SuperHouse/CBMINI/Images/2018-04-11_12-32-10.jpg

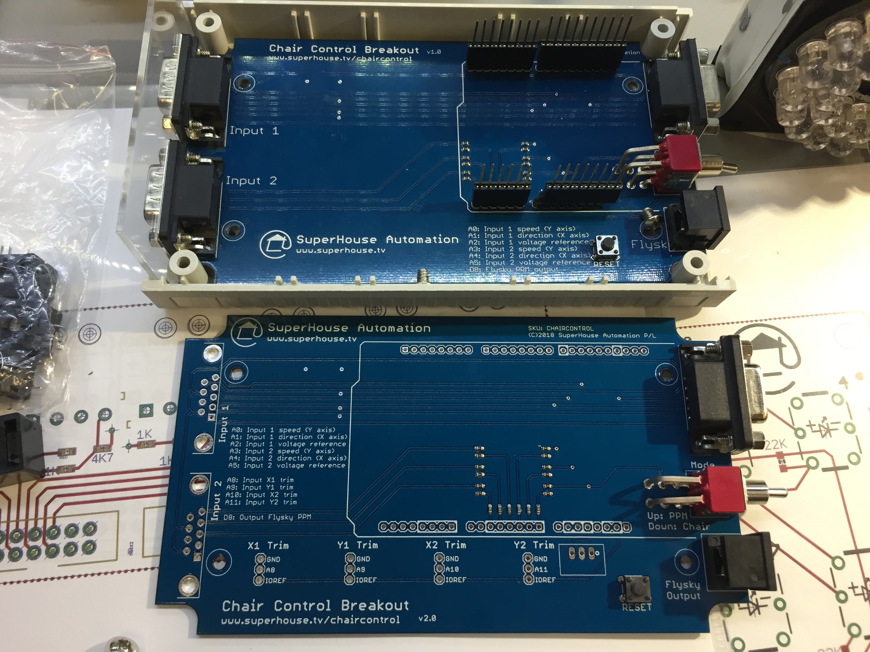
Images/2018-04-11_12-32-10.jpg
