SuperHouse/CBMINI/Images/2018-04-11_17-02-50.jpg

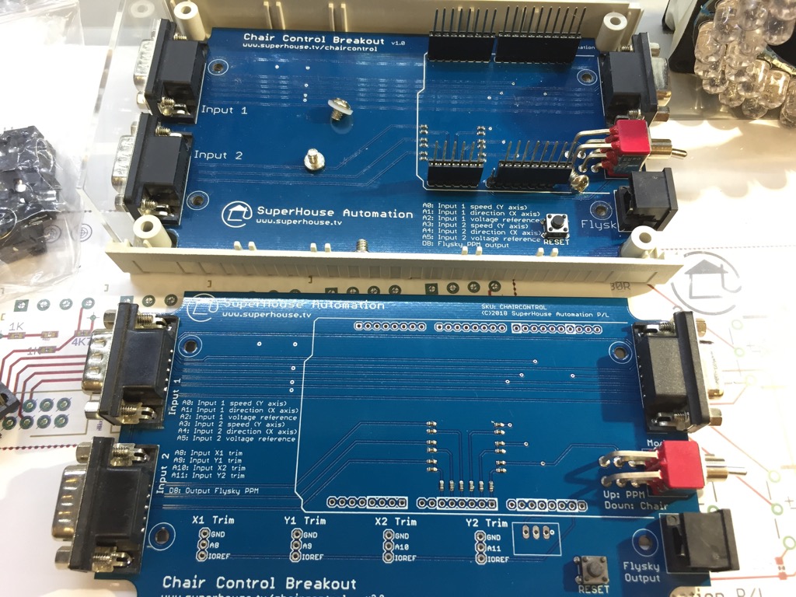
Images/2018-04-11_17-02-50.jpg
