SuperHouse/CBMINI/Images/2018-07-26_15-38-04.jpg

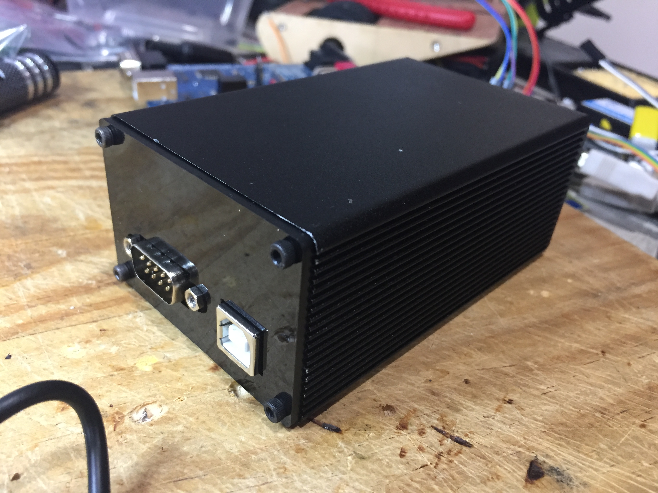
Images/2018-07-26_15-38-04.jpg
