SuperHouse/CBMINI/Images/2018-07-26_15-38-23.jpg

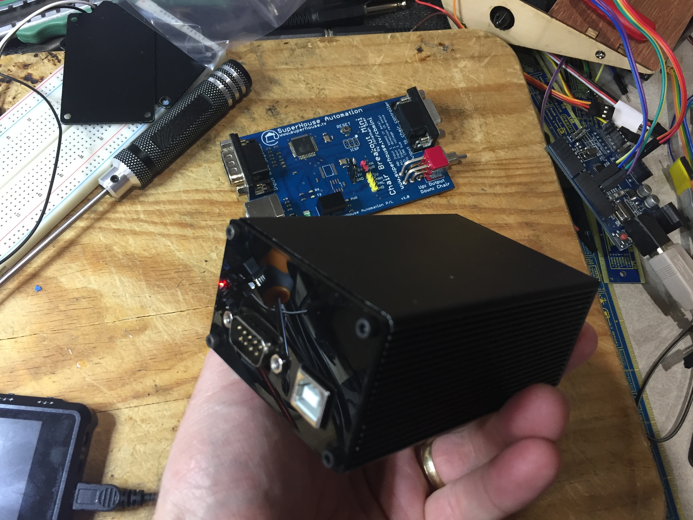
Images/2018-07-26_15-38-23.jpg
