SuperHouse/CBMINI/Images/2018-07-26_15-39-45.jpg

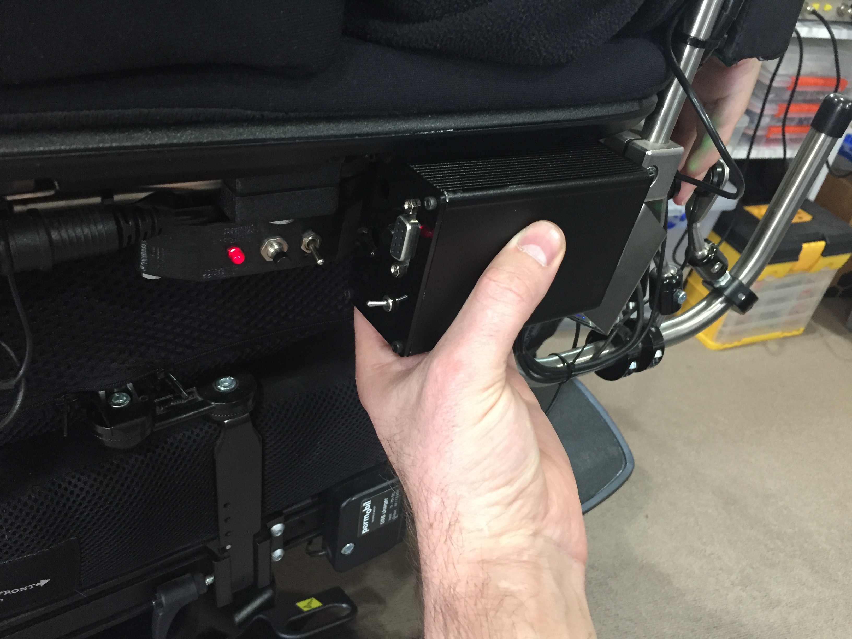
Images/2018-07-26_15-39-45.jpg
