SuperHouse/CBMINI/Images/2018-07-26_15-40-40.jpg

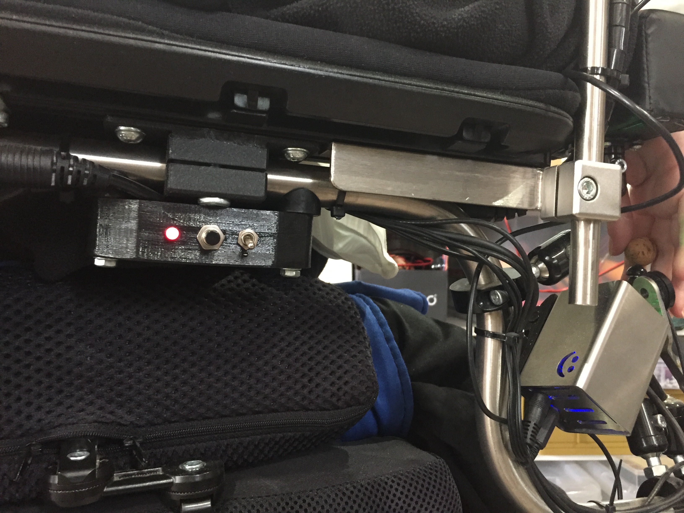
Images/2018-07-26_15-40-40.jpg
