SuperHouse/CBMINI/Images/2018-07-26_15-41-06.jpg

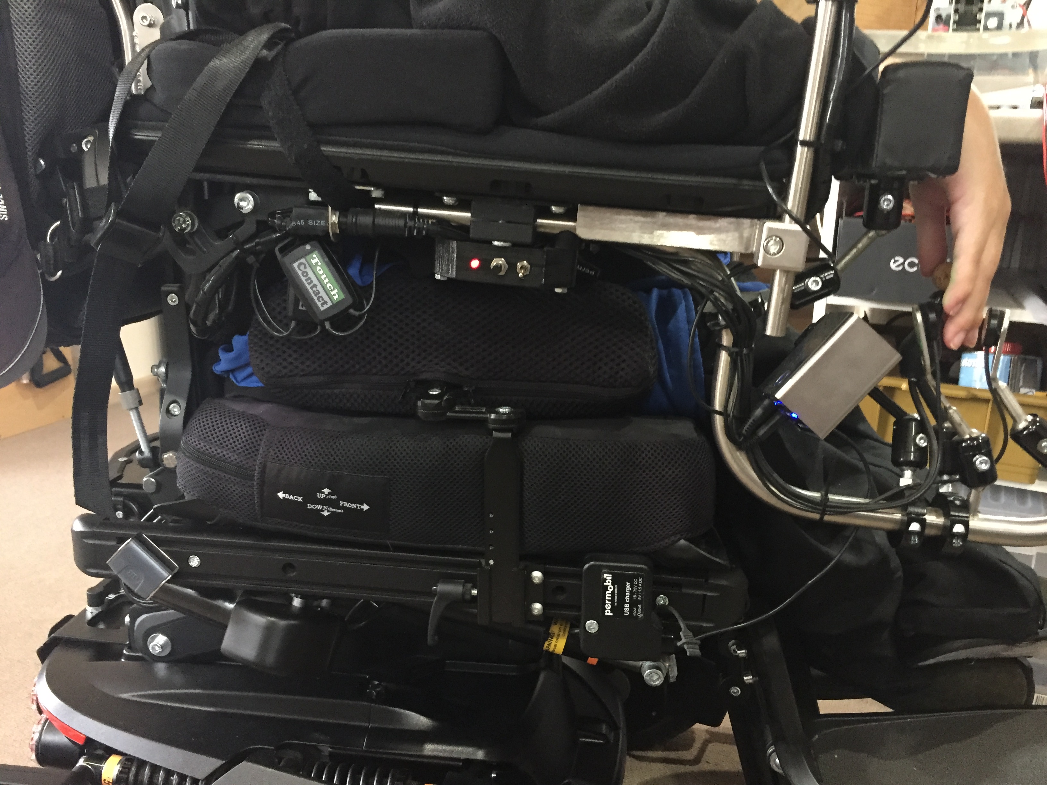
Images/2018-07-26_15-41-06.jpg
