SuperHouse/CBMINI/Images/2018-07-26_15-42-06.jpg

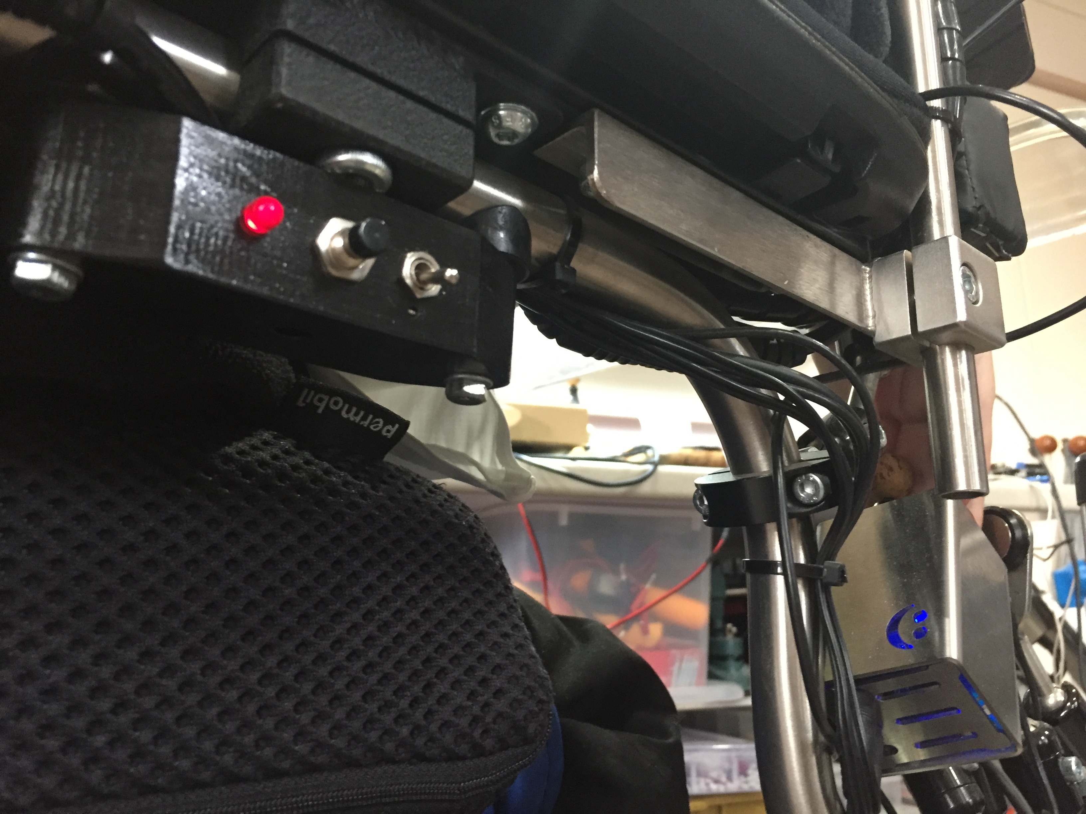
Images/2018-07-26_15-42-06.jpg
