SuperHouse/CBMINI/Images/2018-07-26_15-44-15.jpg

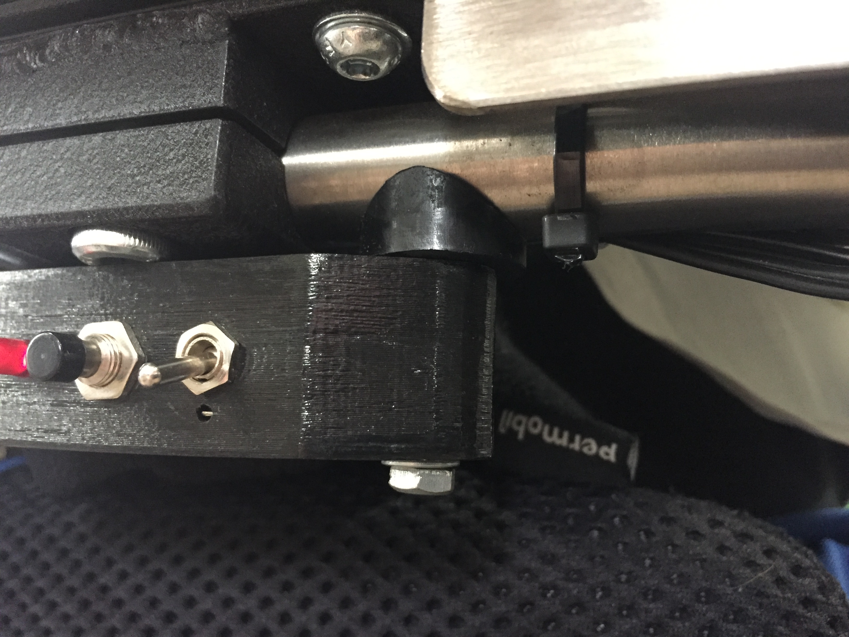
Images/2018-07-26_15-44-15.jpg
