SuperHouse/CBMINI/Images/2018-07-26_15-45-27.jpg

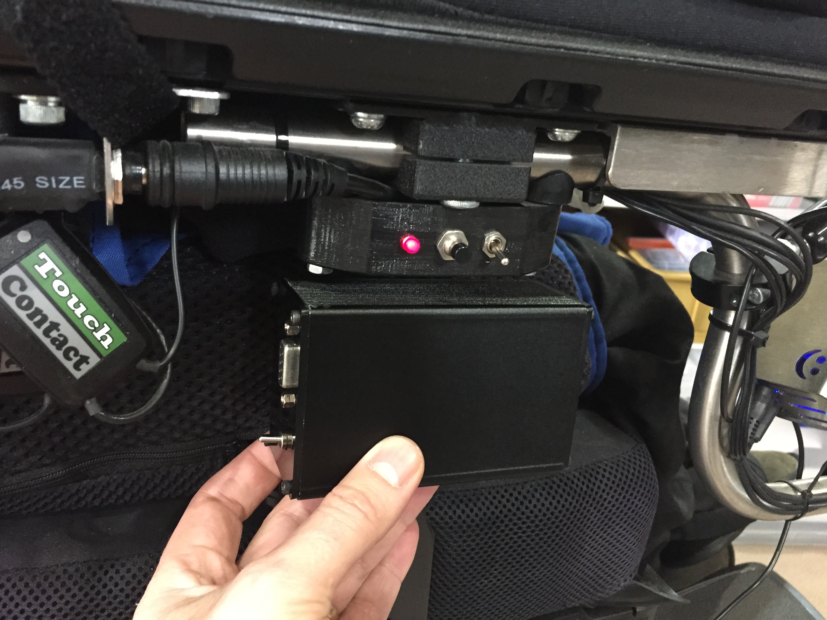
Images/2018-07-26_15-45-27.jpg
