SuperHouse/CBMINI/Images/2018-07-26_16-08-34.jpg

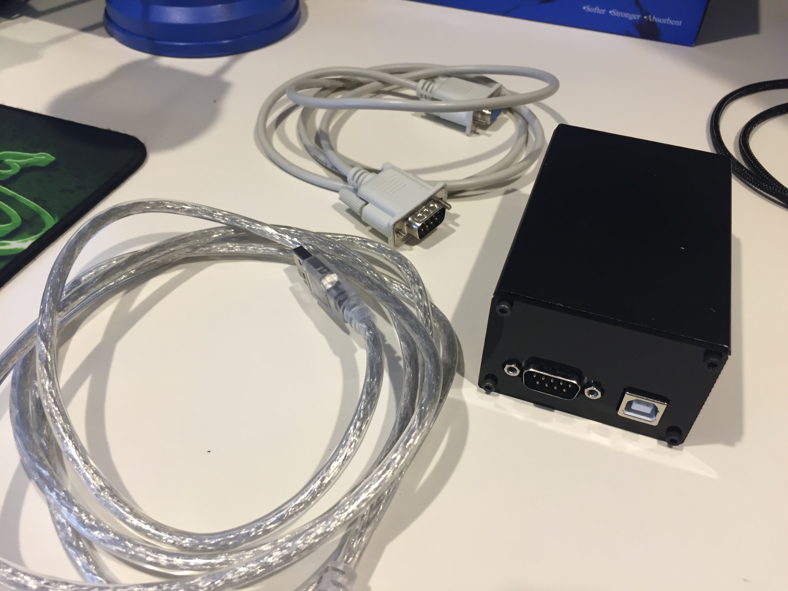
Images/2018-07-26_16-08-34.jpg
