SuperHouse/CBMINI/Images/2018-07-31_14-34-46.jpg

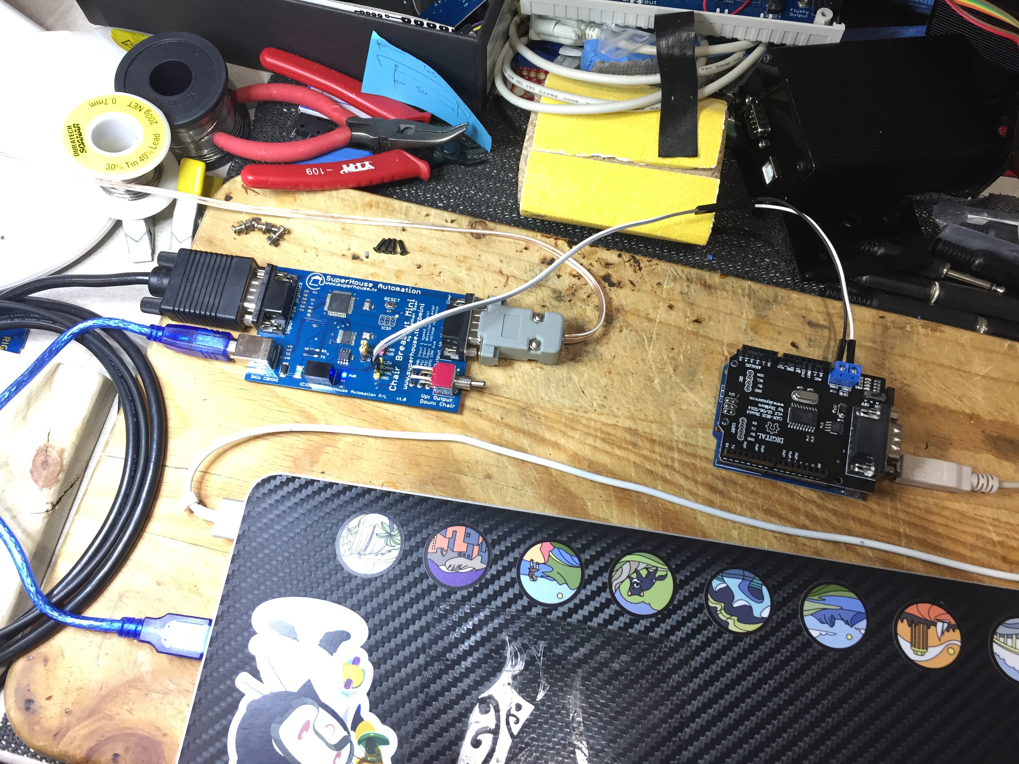
Images/2018-07-31_14-34-46.jpg
