SuperHouse/CBMINI/Images/2018-08-02_20-13-39.jpg

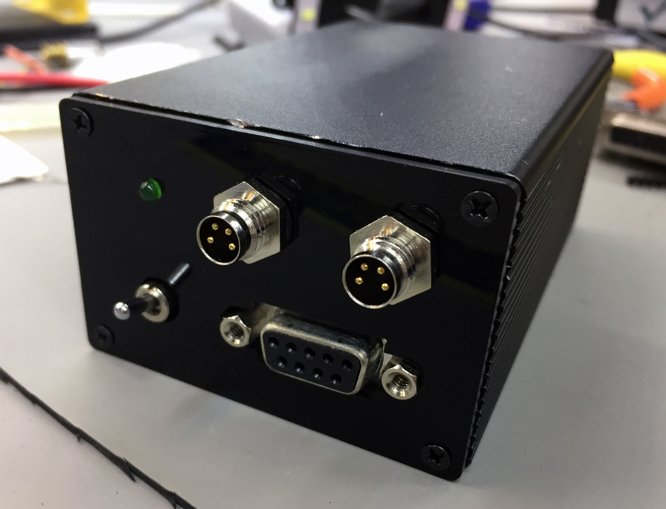
Images/2018-08-02_20-13-39.jpg
