SuperHouse/CBMINI/Images/2019-01-18_22-05-54.jpg

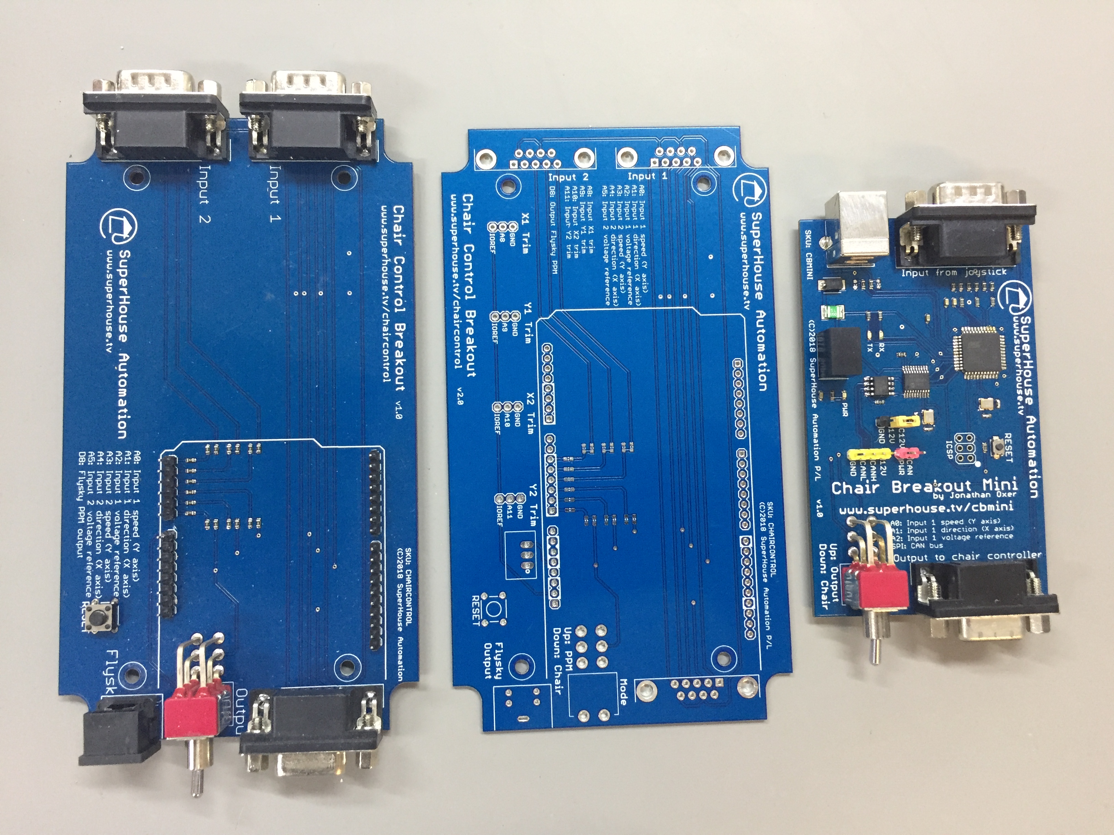
Images/2019-01-18_22-05-54.jpg
