SuperHouse/CBMINI/Images/2019-04-17_09-52-04.jpg

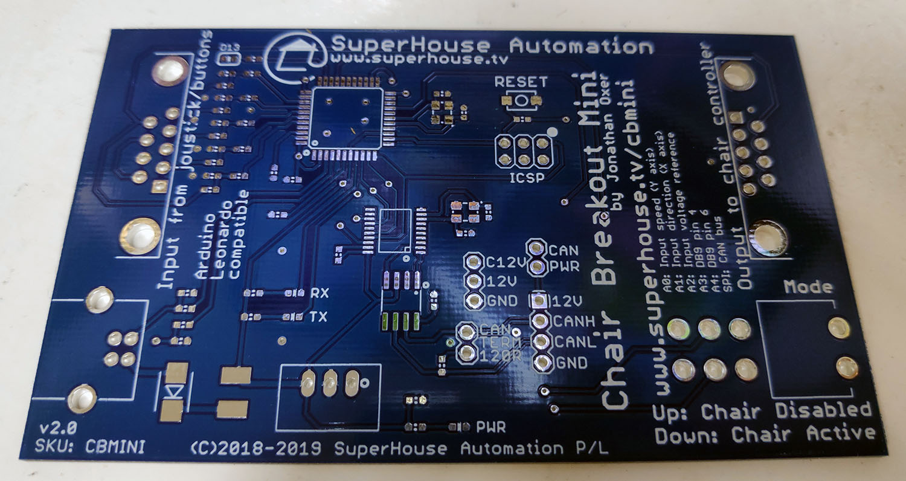
Images/2019-04-17_09-52-04.jpg
