SuperHouse/CBMINI/Images/2019-04-18_10-50-11.jpg

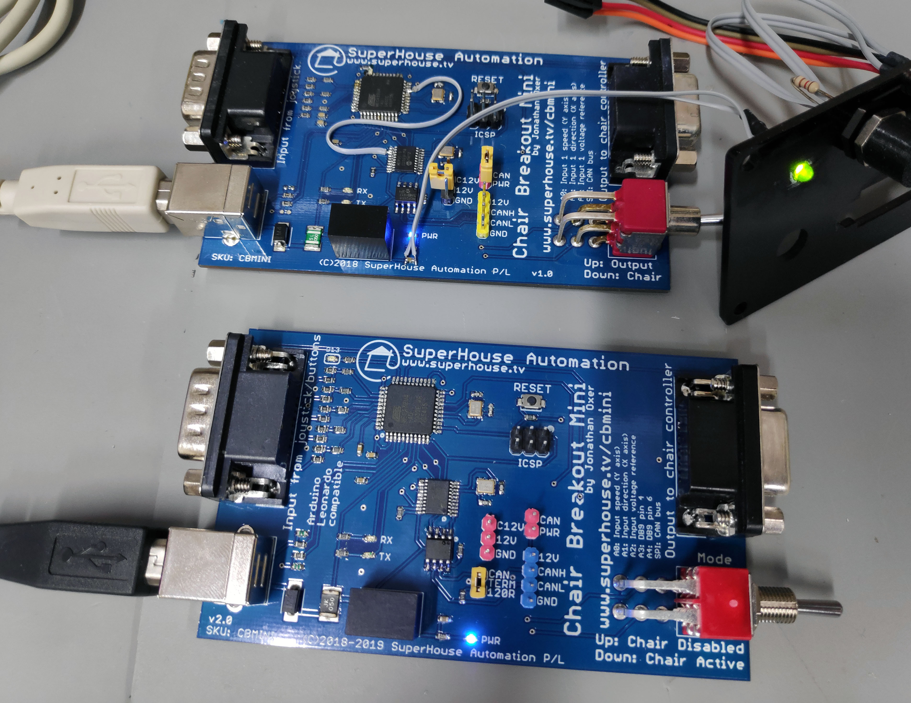
Images/2019-04-18_10-50-11.jpg
