SuperHouse/CBMINI/Images/2019-04-18_11-13-38.jpg

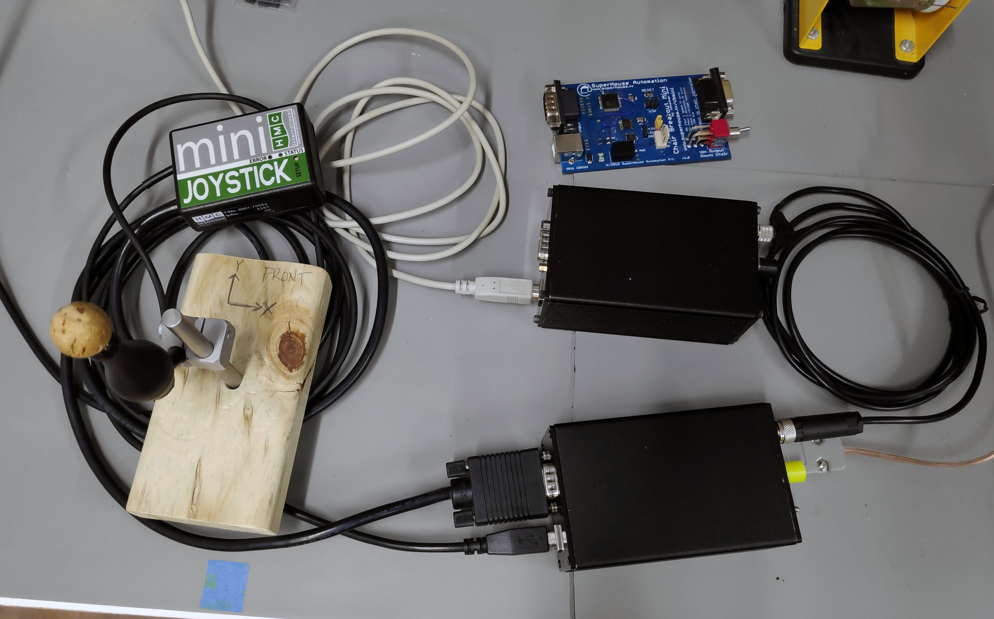
Images/2019-04-18_11-13-38.jpg
