SuperHouse/CBMINI/Images/2019-04-23_15-40-32.jpg

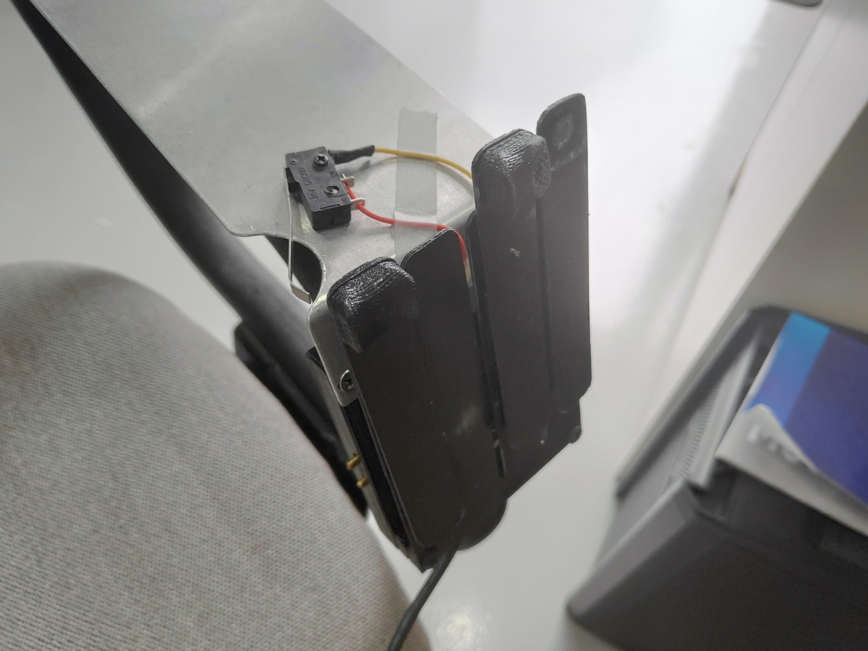
Images/2019-04-23_15-40-32.jpg
