SuperHouse/CBMINI/Images/2019-04-23_15-41-35.jpg

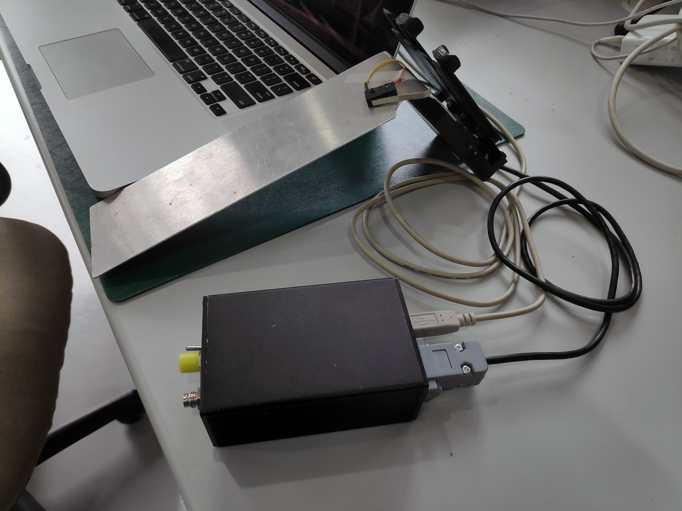
Images/2019-04-23_15-41-35.jpg
